D3SXX/STM32-Battery-Management/docs/KiCAD Files/MosfetPowerControl/image/README/1696499283589.png

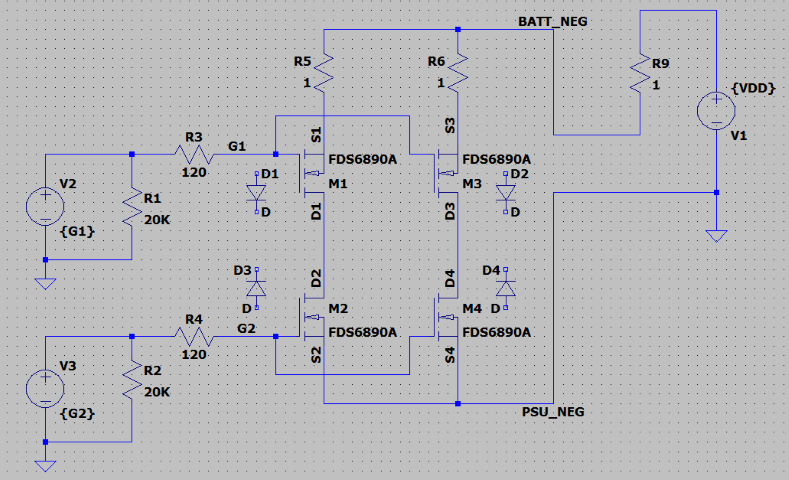
docs/KiCAD Files/MosfetPowerControl/image/README/1696499283589.png
