D3SXX/STM32-Battery-Management/docs/KiCAD Files/MultiCellBatteryMeter/image/README/1696500831667.png

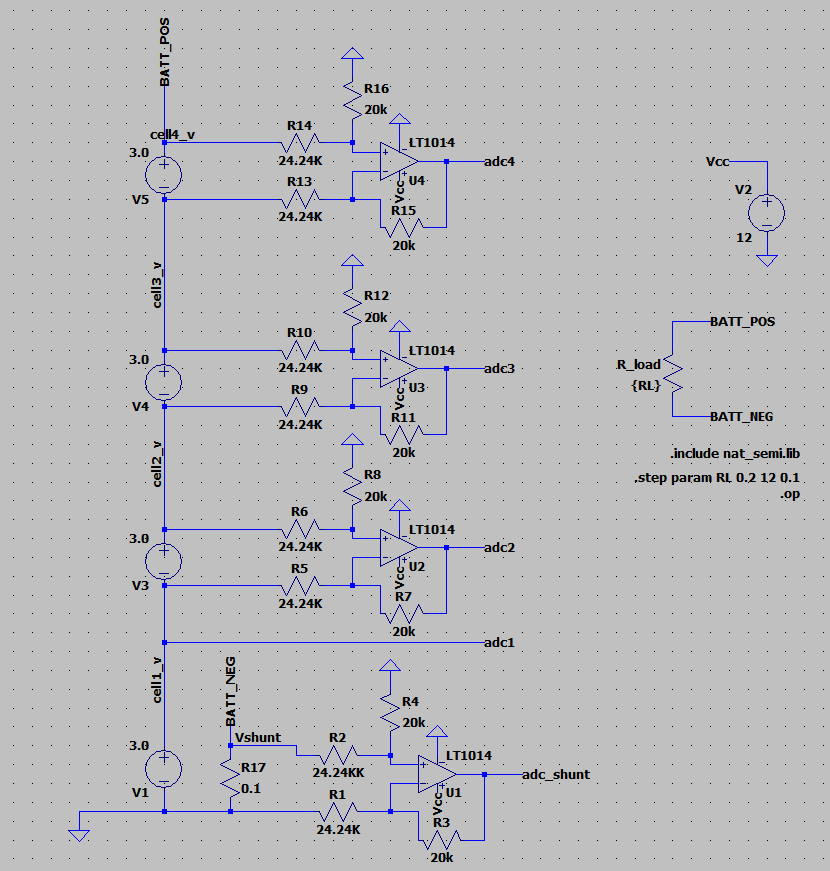
docs/KiCAD Files/MultiCellBatteryMeter/image/README/1696500831667.png
