D3SXX/STM32-Battery-Management/docs/KiCAD Files/MultiCellBatteryMeter/image/README/1696508456106.png

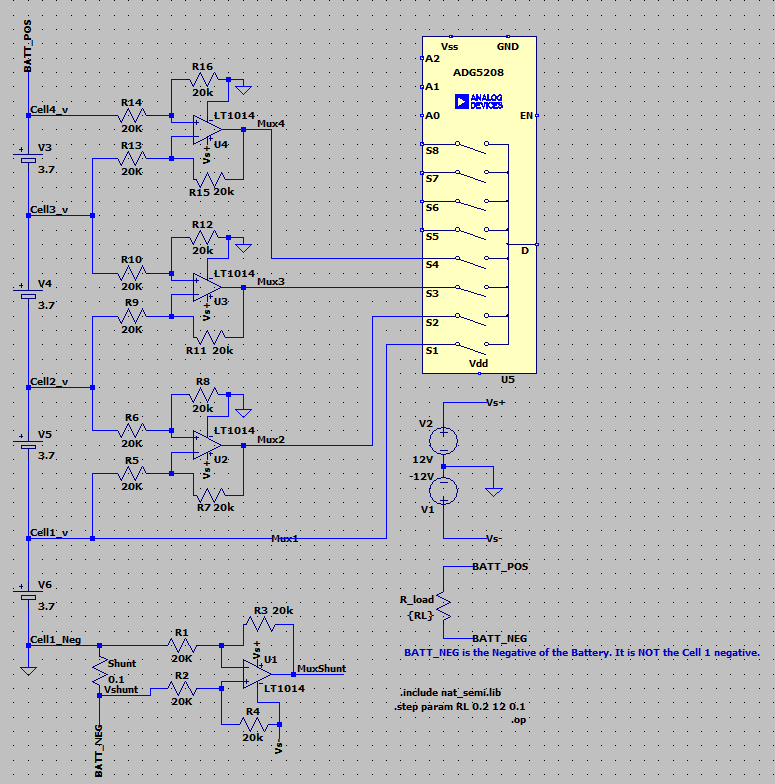
docs/KiCAD Files/MultiCellBatteryMeter/image/README/1696508456106.png
