D3SXX/STM32-Battery-Management/docs/KiCAD Files/MosfetPowerControl/TestSim.asc

MOS_SW: MosfetPowerControl
R1: res; 1R
V1: voltage; 3.3V
V2: battery; {VPSU}
V3: voltage; 0V
Named nets: 0, PSU
.step param VPSU -12 12 1
.op
