D3SXX/STM32-Battery-Management/docs/KiCAD Files/MultiCellBatteryMeter/MultiCellBatteryMeter.asc

R1: res; 20K
R2: res; 20K
R3: res; 20k
R4: res; 20k
R5: res; 20K
R6: res; 20K
R7: res; 20k
R8: res; 20k
R9: res; 20K
R10: res; 20K
R11: res; 20k
R12: res; 20k
R13: res; 20K
R14: res; 20K
R15: res; 20k
R16: res; 20k
R17: res; 48.48K
R18: res; 48.48K
R19: res; 20k
R20: res; 10k
R21: res; 20k
R22: res; 20k
R23: res; 94.25K
R24: res; 20K
Shunt: res; 0.1; pwr=10W
U1: opamp2; LM324/NS
U5: ADG5208
U6: opamp2; LM324/NS
U7: opamp2; LM324/NS
U9: opamp2; LM324/NS
U10: opamp2; LM324/NS
U11: opamp2; LM324/NS
Named nets: Vs+, C1_P, C2_P, C3_P, C4_P, Mux2, Mux3, Mux4, Mux1, Vshunt, Vs-, GND, MUX_Out, BATT_P, ShuntOut, SEL0, SEL1, SEL2, EN
.include nat_semi.lib
Discharging: -4V - 0V
Charging: 0 - 4V
4V
0-8V => 0-3.3V
12V
+/-40A
0-3.3V
0-4V
0-3.3V
0-4V
0-4V
0-4V
0-4V
3.3V
3.3V
Discharging: -20A - 0A
Charging: 0A - 20A
0-3.3V
0-1.65V => Charing 20V - 0V
1.65V => 3.3V Discharging 0V-20V
0-8V
0-4V => Charing 20 - 0A
4-8V => 3.3V Discharging 0-20A
