D3SXX/STM32-Battery-Management/docs/KiCAD Files/MultiCellBatteryMeter/MultiCellBatteryMeterBlockSim.asc

R1: res; {R_LOAD}
V1: cell; 4V
V2: cell; 4V
V3: cell; 4V
V4: cell; 4V
V5: voltage; 12V
V6: voltage; -12V
V7: voltage; 3.3V
X1: MultiCellBatteryMeter
Named nets: 0, Cell1_v, Cell2_v, Cell3_v, Cell4_v, BATT_NEG, Vs+, Vs-, TRUE, MUX_OUT, SHUNT_OUT
.include nat_semi.lib
.step param R_LOAD 0.3 160 10
.op
Discharging Simulation
Discharging Current: 0-20A
V_shunt: 0 - 1.65V
SEL: 0x01
Cell1_V: 4V
MUX_OUT: 3.3V
