D3SXX/STM32-Battery-Management/docs/KiCAD Files/MultiCellBatteryMeter/MultiCellBatteryMeterSim.asc

R1: res; 50R
R17: res; 20K
R18: res; 20K
R19: res; 20k
R20: res; 20k
R21: res; 20K
R22: res; 20K
R23: res; 20k
R24: res; 20k
R25: res; 20K
R26: res; 20K
R27: res; 20k
R28: res; 20k
R29: res; 20K
R30: res; 20K
R31: res; 20k
R32: res; 20k
R33: res; 48.48K
R34: res; 48.48K
R35: res; 20k
R36: res; 10k
R37: res; 20k
R38: res; 20k
R39: res; 94.25K
R40: res; 20K
R_load: res; 100R
Shunt1: res; 0.1; pwr=10W
U6: ADG5208
U7: opamp2; LM324/NS
U8: opamp2; LM324/NS
U9: opamp2; LM324/NS
U10: opamp2; LM324/NS
U11: opamp2; LM324/NS
U12: opamp2; LM324/NS
V1: voltage; -12V
V2: voltage; 12V
V3: cell; 4V
V4: cell; 4V
V5: cell; 4V
V6: cell; 4V
V7: voltage; 3.3V
V8: voltage; {VSIM}
Named nets: 0, Vs+, Cell1_v, Cell2_v, Cell3_v, Cell4_v, BATT_NEG, BATT_POS, Cell1_Neg, Vs-, C1_P, C2_P, C3_P, C4_P, Mux2, Mux3, Mux4, Mux1, Vshunt, GND, MUX_Out, ShuntOut, SEL0, EN, TRUE, SEL1, SEL2
BATT_NEG is the Negative of the Battery. It is NOT the Cell 1 negative.
.include nat_semi.lib
+/- 4V
4V
0-8V => 0-3.3V
12V
+/-40A
0-3.3V
0-1.65V => Charing 20V - 0V
1.65V => 3.3V Discharging 0V-20V
0-4V
0-3.3V
.step param VSIM -2000 2000 200
.op
