D3SXX/STM32-Battery-Management/docs/KiCAD Files/MosfetPowerControl/MosfetPowerControlSim.asc

D1: diode
D2: diode
D3: diode
D4: diode
M1: nmos; FDS6890A
M2: nmos; FDS6890A
M3: nmos; FDS6890A
M4: nmos; FDS6890A
R1: res; 20K
R2: res; 20K
R3: res; 120
R4: res; 120
R5: res; 2.2
R6: res; 2.2
R9: res; 1
V1: voltage; {VDD}
V2: voltage; {G1}
V3: voltage; {G2}
Named nets: 0, G1, G2, D2, D1, D3, D4, S1, S2, S4, S3, BATT_NEG, PSU_NEG
.step param VDD list -12 0 12
.op
