D3SXX/STM32-Battery-Management/docs/KiCAD Files/MosfetPowerControl/MosfetPowerControl.asc

M1: nmos; FDS6890A
M2: nmos; FDS6890A
M3: nmos; FDS6890A
M4: nmos; FDS6890A
R1: res; 20K
R2: res; 20K
R3: res; 120
R4: res; 120
R5: res; 1
R6: res; 1
R9: res; 1
V1: voltage; 20
V2: voltage; {VC}
V3: voltage; {VC}
Named nets: 0, G1, G2
.step param VC 0 20 0.1
.op
