D3SXX/STM32-Battery-Management/docs/KiCAD Files/MosfetPowerControl/sim_ltspice/MosfetPowerControl.asc

M1: nmos; FDS6890A
M2: nmos; FDS6890A
M3: nmos; FDS6890A
M4: nmos; FDS6890A
R1: res; 20K
R2: res; 20K
R3: res; 120
R4: res; 120
R5: res; 2.2
R6: res; 2.2
Named nets: G1, G2, D2, D1, D3, D4, S1, S2, S4, S3, BATT_N, PSU_N, G1_IN, G2_IN, GND
.include nat_semi.lib
