D3SXX/STM32-Battery-Management/test/embedded/test_adc/test_adc.c

#include <unity.h>

#include "../unity_config.h"
#include "adc.h"
#include "adc_utils.h"
#include "moc_adc_read.h"
#include "stm32l1xx.h"
#include "usart_config.h"

void setUp(void) {
    // set stuff up here
}

void tearDown(void) {
    // clean stuff up here
}

void test_adc_convert_batt_current_positive(void) {
    uint16_t adc_value = 0;
    uint16_t current   = 0;
    moc_adc_set(3732);  // should be 37590mA
    adc_value = moc_adc_read((uint8_t)0xff);
    current   = adc_convert_batt_current(adc_value);
    TEST_ASSERT_EQUAL((uint16_t)37593, current);
}

void test_adc_convert_batt_current_negative(void) {
    uint16_t adc_value = 0;
    uint16_t current   = 0;
    moc_adc_set(3733);
    adc_value = moc_adc_read((uint8_t)0xff);
    current   = adc_convert_batt_current(adc_value);
    TEST_ASSERT_NOT_EQUAL((uint16_t)37600, current);
}

void test_adc_convert_batt_current_edge_max(void) {
    uint16_t adc_value = 0;
    uint16_t current   = 0;
    moc_adc_set(4095);
    adc_value = moc_adc_read((uint8_t)0xff);
    current   = adc_convert_batt_current(adc_value);
    TEST_ASSERT_EQUAL((uint16_t)41250, current);
}

void test_adc_convert_batt_current_edge_min(void) {
    uint16_t adc_value = 0;
    uint16_t current   = 0;
    moc_adc_set(0);
    adc_value = moc_adc_read((uint8_t)0xff);
    current   = adc_convert_batt_current(adc_value);
    TEST_ASSERT_EQUAL((uint16_t)0, current);
}

void test_adc_convert_cell_voltage_positive(void) {
    uint16_t volta = 0;
    moc_adc_set(3623);
    uint16_t adc_value = moc_adc_read(0);
    volta = adc_convert_cell_voltage(adc_value);
    TEST_ASSERT_EQUAL((uint16_t)3649, volta);
}

void test_adc_convert_cell_voltage_negatitive(void) {
    uint16_t volta = 0;
    moc_adc_set(3624);
    uint16_t adc_value = moc_adc_read(0);
    volta = adc_convert_cell_voltage(adc_value);
    TEST_ASSERT_NOT_EQUAL((uint16_t)3649, volta);
}

void test_adc_convert_cell_voltage_edge_max(void) {
    uint16_t volta = 0;
    moc_adc_set(4095);
    uint16_t adc_value = moc_adc_read(0);
    volta = adc_convert_cell_voltage(adc_value);
    TEST_ASSERT_EQUAL((uint16_t)4125, volta);
}

void test_adc_convert_cell_voltage_edge_min(void) {
    uint16_t volta = 0;
    moc_adc_set(4095);
    uint16_t adc_value = moc_adc_read(0);
    volta = adc_convert_cell_voltage(adc_value);
    TEST_ASSERT_EQUAL((uint16_t)4125, volta);
}

void test_adc_convert_temperature_positive(void) {
    uint16_t temp_int = 0;
    moc_adc_set(1241);
    uint16_t adc_value = moc_adc_read(0);
    temp_int = adc_convert_batt_temp(adc_value);
    TEST_ASSERT_EQUAL(1000, temp_int);
}

void test_adc_convert_temperature_negative(void) {
    uint16_t temp_int = 0;
    moc_adc_set(1240);
    uint16_t adc_value = moc_adc_read(0);
    temp_int = adc_convert_batt_temp(adc_value);
    TEST_ASSERT_NOT_EQUAL(1000, temp_int);
}

void test_adc_convert_temperature_edge_max(void) {
    uint16_t temp_int = 0;
    moc_adc_set(4095);
    uint16_t adc_value = moc_adc_read(0);
    temp_int = adc_convert_batt_temp(adc_value);
    TEST_ASSERT_EQUAL(3300, temp_int);
}

void test_adc_convert_temperature_edge_min(void) {
    uint16_t temp_int = 0;
    moc_adc_set(0);
    uint16_t adc_value = moc_adc_read(0);
    temp_int = adc_convert_batt_temp(adc_value);
    TEST_ASSERT_EQUAL(0, temp_int);
}

static inline void LED2_init(void) {
    RCC->AHBENR |= RCC_AHBENR_GPIOAEN;              // GPIOA ABH bus clock ON. p154
    GPIOA->MODER |= 0x01 << GPIO_MODER_MODER5_Pos;  // GPIOA pin 5 to output. p184
    GPIOA->ODR |= 0x20;
}

int main(int argc, char **argv) {
    HAL_Init();       // initialize the HAL library
    HAL_Delay(2000);  // service delay
    LED2_init();

    UNITY_BEGIN();
    RUN_TEST(test_adc_convert_batt_current_positive);
    GPIOA->ODR ^= 0x20;
    HAL_Delay(500);
    RUN_TEST(test_adc_convert_batt_current_negative);
    GPIOA->ODR ^= 0x20;
    HAL_Delay(500);
    RUN_TEST(test_adc_convert_batt_current_edge_max);
    GPIOA->ODR ^= 0x20;
    HAL_Delay(500);
    RUN_TEST(test_adc_convert_batt_current_edge_min);
    GPIOA->ODR ^= 0x20;
    HAL_Delay(500);
    RUN_TEST(test_adc_convert_cell_voltage_positive);
    GPIOA->ODR ^= 0x20;
    HAL_Delay(500);
    RUN_TEST(test_adc_convert_cell_voltage_negatitive);
    GPIOA->ODR ^= 0x20;
    HAL_Delay(500);
    RUN_TEST(test_adc_convert_cell_voltage_edge_max);
    GPIOA->ODR ^= 0x20;
    HAL_Delay(500);
    RUN_TEST(test_adc_convert_cell_voltage_edge_min);
    GPIOA->ODR ^= 0x20;
    HAL_Delay(500);
    RUN_TEST(test_adc_convert_temperature_positive);
    GPIOA->ODR ^= 0x20;
    HAL_Delay(500);
    RUN_TEST(test_adc_convert_temperature_negative);
    GPIOA->ODR ^= 0x20;
    HAL_Delay(500);
    RUN_TEST(test_adc_convert_temperature_edge_max);
    GPIOA->ODR ^= 0x20;
    HAL_Delay(500);
    RUN_TEST(test_adc_convert_temperature_edge_min);
    GPIOA->ODR ^= 0x20;
    HAL_Delay(500);
    UNITY_END();

    while (1) {
    }
}

void SysTick_Handler(void) { HAL_IncTick(); }
